ferre111/Simple-watch-on-stm32/Core/app/pages/inc/images.h

/*
 * images.h
 *
 *  Created on: Dec 2, 2020
 *      Author: Administrator
 */

#pragma once

#include "main.h"

//----------------------------------------------------------------------

/*Main compass image*/
extern const uint8_t compassImage[290];

/*Main spirit level image*/
extern const uint8_t spirit_level_image[1026];

/*Spirit level pointer image*/
extern const uint8_t spirit_level_pointer[7];

extern const uint8_t battery_zero[];
extern const uint8_t battery_quarter[];
extern const uint8_t battery_half[];
extern const uint8_t battery_full[];

extern const uint8_t padlock_close[];
extern const uint8_t padlock_open[];
